dennis-lawter/pico-pet/embedded/src/game/hardware/input.rs

/// The number of frames a key must be held before key_repeat_triggered = true
const KEY_REPEAT_FRAMES: usize = 5;

/// The state of a key is comprised of several flags and a held frame count
/// The key state is polled at the start of each game loop.
/// This can rarely cause a failure to register a keypress,
/// if it wasn't pressed during that poll.
/// We poll at the framerate,
/// so this can occur at low framerates,
/// but it is extremely infrequent above 20fps.
#[derive(Default)]
pub struct KeyState {
    pub is_down: bool,
    pub was_down: bool,
    pub just_pressed: bool,
    pub just_released: bool,
    pub key_held_frames: usize,
    pub key_repeat_triggered: bool,
}

impl KeyState {
    /// Updates the key state for the frame,
    /// with information about if the key was down during the poll.
    fn update(&mut self, is_down: bool) {
        self.was_down = self.is_down;
        self.is_down = is_down;
        self.just_pressed = !self.was_down && is_down;
        self.just_released = self.was_down && !is_down;
        if is_down {
            self.key_held_frames += 1;
        } else {
            self.key_held_frames = 0;
        }
        self.key_repeat_triggered = self.key_held_frames % KEY_REPEAT_FRAMES == 1;
    }
}

#[derive(Clone)]
pub enum KeyNames {
    Back = 0,
    Left,
    Right,
    Confirm,
    Clock,

    /// Evaluates to the count of enum varaints, useful for array sizing
    Count,
}
impl Into<usize> for KeyNames {
    fn into(self) -> usize {
        self as usize
    }
}

#[derive(Default)]
pub struct InputHandler {
    pub keys: [KeyState; KeyNames::Count as usize],
}

impl InputHandler {
    /// Polls for each key's pressed status then runs the keystate update.
    pub fn update(&mut self) {
        let hardware = crate::game::globals::get_hardware();
        let key_positions = [
            hardware.key0_pressed(),
            hardware.key1_pressed(),
            hardware.key2_pressed(),
            hardware.key3_pressed(),
            hardware.clock_high(),
        ];
        for i in 0..self.keys.len() {
            self.keys[i].update(key_positions[i]);
        }
    }

    /// Resets all KeyStates.
    /// Currently used for the idle state.
    pub fn force_reset(&mut self) {
        for i in 0..self.keys.len() {
            self.keys[i].update(false);
            self.keys[i].update(false);
        }
    }

    /// Queries for a specific key's KeyState.
    pub fn get_state(&self, name: &KeyNames) -> &KeyState {
        &self.keys[name.clone() as usize]
    }
}
